agentk/phrettboard/images/guts-2.jpeg

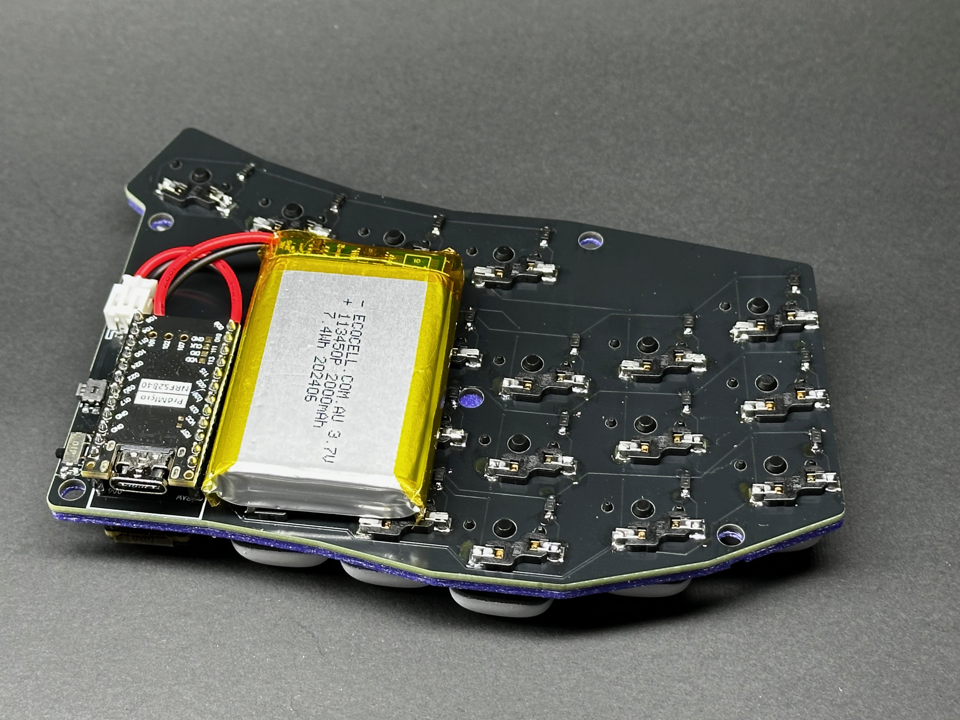
images/guts-2.jpeg
