agentk/phrettboard/images/purple-2.jpeg

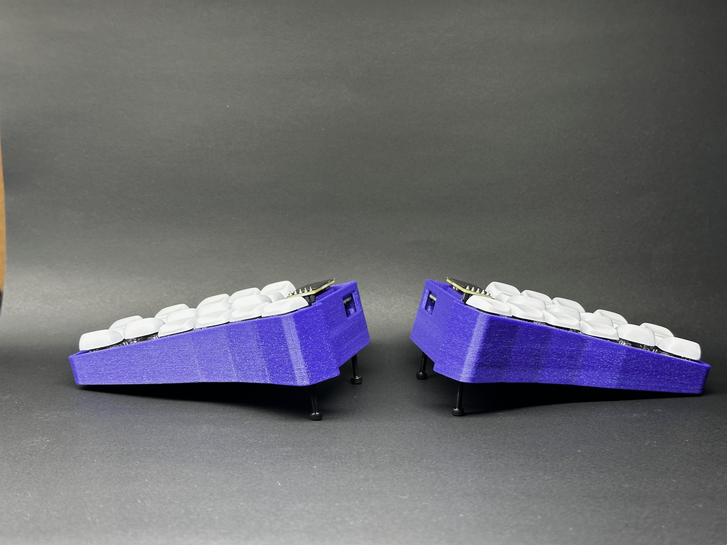
images/purple-2.jpeg
