agentk/phrettboard/images/purple-3.jpeg

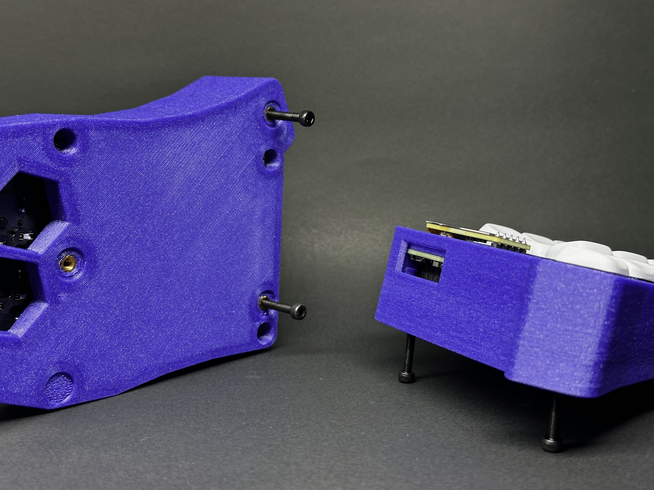
images/purple-3.jpeg
