agentk/phrettboard/images/purple-5.jpeg

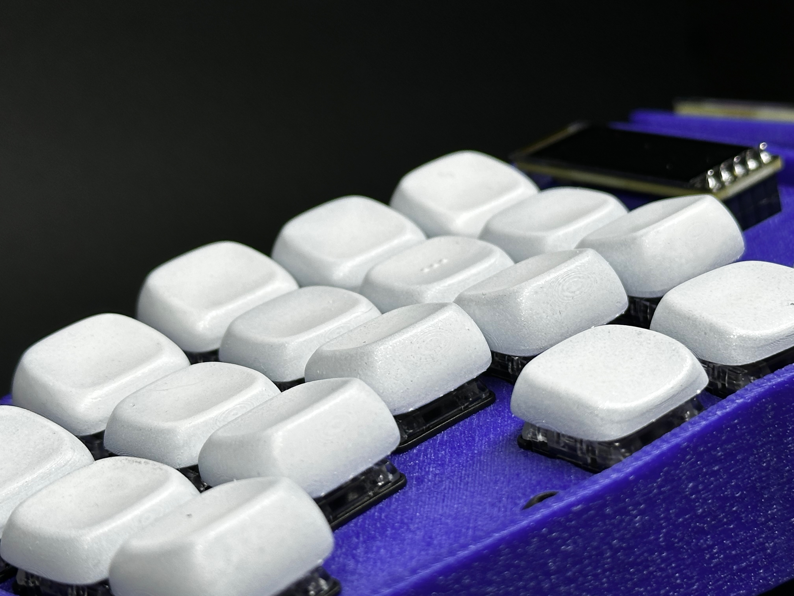
images/purple-5.jpeg
