agentk/phrettboard/images/toxic-vertical.jpeg

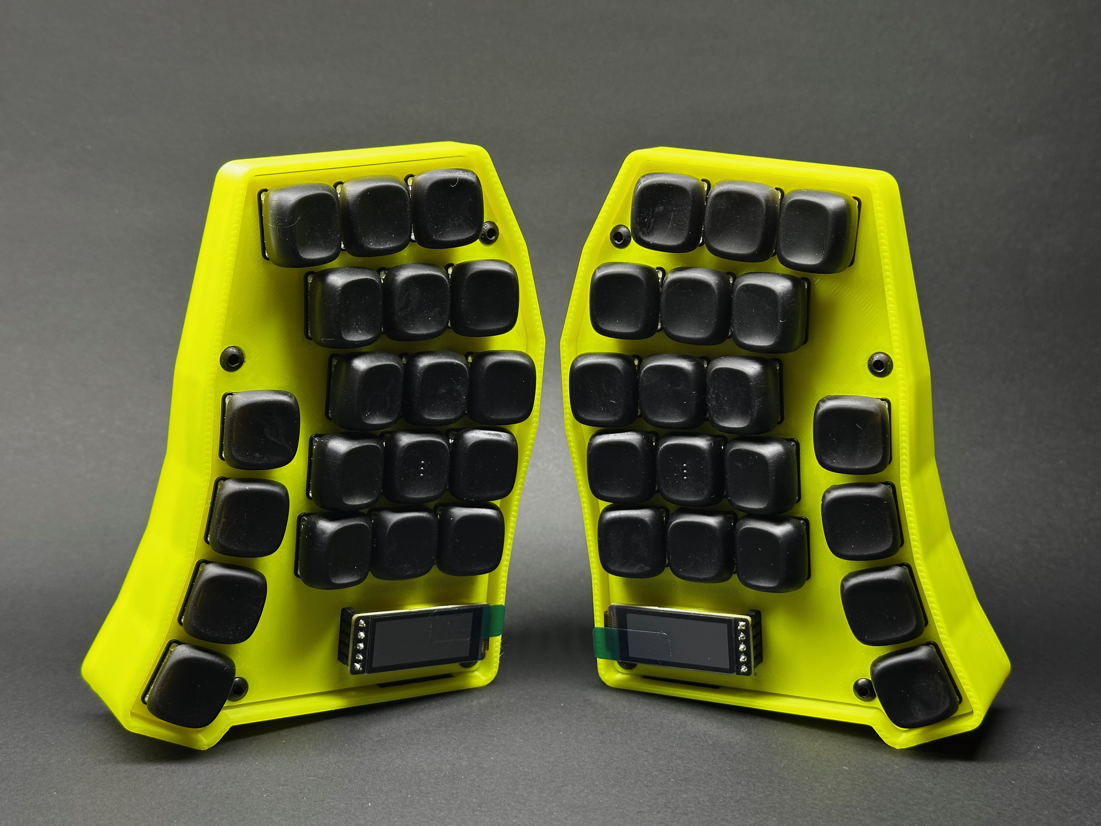
images/toxic-vertical.jpeg
