agentk/phrettboard/images/travel-case-2.jpeg

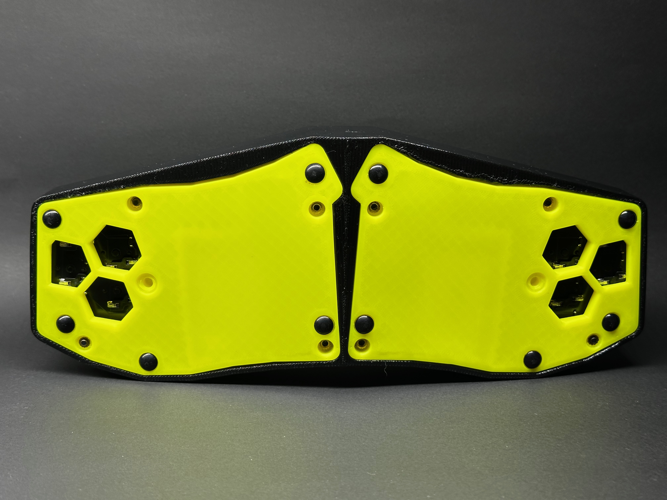
images/travel-case-2.jpeg
