agentk/phrettboard/images/travel-case-3.jpeg

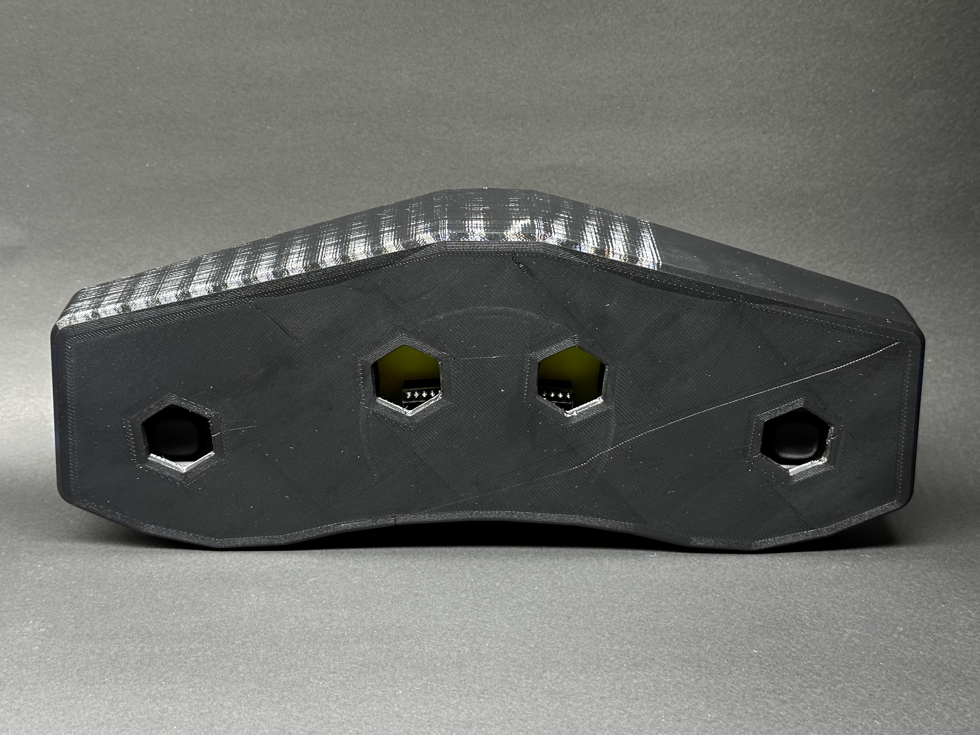
images/travel-case-3.jpeg
