agentk/phrettboard/images/travel-case-4.jpeg

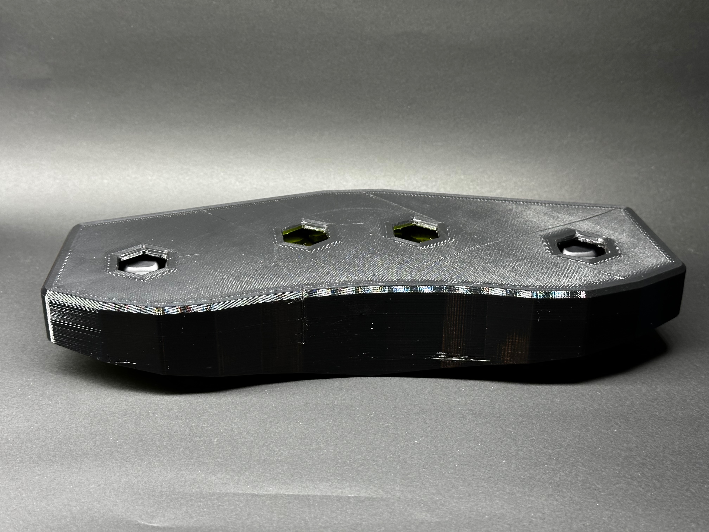
images/travel-case-4.jpeg
